rbray89/usbpov/usbPOV-src/i2cmaster.c

#include "i2cmaster.h"

void i2c_init(void)
{
  //CPU_clock/(16 + 2*TWBR*(4^prescaler))
  
  // Initial ATMega328P TWI/I2C Peripheral
  TWSR = 0x00;         // Select Prescaler of 0

  //8000000/(16 + 2*TWBR*(4^prescaler))
  TWBR = 0x04;        // 4 Decimal
}

/* START I2C Routine */
unsigned char i2c_transmit(unsigned char type) {
  switch(type) {
     case I2C_START:    // Send Start Condition
       TWCR = (1 << TWINT) | (1 << TWSTA) | (1 << TWEN);
       break;
     case I2C_DATA:     // Send Data with No-Acknowledge
       TWCR = (1 << TWINT) | (1 << TWEN);
       break;
     case I2C_DATA_ACK: // Send Data with Acknowledge
       TWCR = (1 << TWEA) | (1 << TWINT) | (1 << TWEN);
       break;
     case I2C_STOP:     // Send Stop Condition
	TWCR = (1 << TWINT) | (1 << TWEN) | (1 << TWSTO);
	return 0;
  }

  // Wait for TWINT flag set on Register TWCR

  while (!(TWCR & (1 << TWINT)));

  // Return TWI Status Register, mask the prescaler bits (TWPS1,TWPS0)
  return (TWSR & 0xF8);
}

char i2c_start(unsigned int dev_addr, unsigned char rw_type)
{
  unsigned char n = 0;
  unsigned char twi_status;
  char r_val = -1;

i2c_retry:
  if (n++ >= MAX_TRIES) return r_val;

  // Transmit Start Condition
  twi_status=i2c_transmit(I2C_START);

  // Check the TWI Status
  if (twi_status == TW_MT_ARB_LOST) goto i2c_retry;
  if ((twi_status != TW_START) && (twi_status != TW_REP_START)) goto i2c_quit;

  // Send slave address (SLA_W)
  TWDR = dev_addr | rw_type;

  // Transmit I2C Data
  twi_status=i2c_transmit(I2C_DATA);

  // Check the TWSR status
  if ((twi_status == TW_MT_SLA_NACK) || (twi_status == TW_MT_ARB_LOST)) goto i2c_retry;
  if (twi_status != TW_MT_SLA_ACK) goto i2c_quit;

  r_val=0;

i2c_quit:
  return r_val;
}

void i2c_stop(void)
{
  unsigned char twi_status;

  // Transmit I2C Data
  twi_status=i2c_transmit(I2C_STOP);
}

char i2c_write(char data)
{
  unsigned char twi_status;
  char r_val = -1;

  // Send the Data to I2C Bus
  TWDR = data;

  // Transmit I2C Data
  twi_status=i2c_transmit(I2C_DATA);

  // Check the TWSR status
  if (twi_status != TW_MT_DATA_ACK) goto i2c_quit;

  r_val=0;

i2c_quit:
  return r_val;
}

char i2c_read(char *data,char ack_type)
{
  unsigned char twi_status;
  char r_val = -1;               

  if (ack_type) {
    // Read I2C Data and Send Acknowledge
    twi_status=i2c_transmit(I2C_DATA_ACK);

    if (twi_status != TW_MR_DATA_ACK) goto i2c_quit;
  } else {

    // Read I2C Data and Send No Acknowledge
    twi_status=i2c_transmit(I2C_DATA);

    if (twi_status != TW_MR_DATA_NACK) goto i2c_quit;
  }

  // Get the Data
  *data=TWDR;
  r_val=0;

i2c_quit:
  return r_val;
}
